lliont/lion32/llcc/clib.asm

data
export _fstatus
align 4
LABELV _fstatus
byte 4 1
byte 4 1
byte 4 1
byte 4 1
byte 4 1
skip 48
export _cnt
align 4
LABELV _cnt
byte 4 0
export _arg1
align 1
LABELV _arg1
byte 1 42
byte 1 0
export FMEMORG
align 4
LABELV FMEMORG
byte 4 18532
export FMEMLOWL
align 4
LABELV FMEMLOWL
byte 4 18538
export ftab
align 4
LABELV ftab
byte 4 18600
export abort
code
proc abort 0 0
CNSTI4 0
RETI4
LABELV $1
endproc abort 0 0
export parse
proc parse 48 4
ADDRLP4 0
CNSTI4 1
ASGNI4
LABELV $3
ADDRLP4 0
INDIRI4
CNSTI4 2
LSHI4
ADDRGP4 _vec
ADDP4
CNSTP4 0
ASGNP4
LABELV $4
ADDRLP4 0
ADDRLP4 0
INDIRI4
CNSTI4 1
ADDI4
ASGNI4
ADDRLP4 0
INDIRI4
CNSTI4 12
LTI4 $3
ADDRLP4 8
CNSTI4 0
ASGNI4
ADDRLP4 0
ADDRLP4 8
INDIRI4
ASGNI4
ADDRLP4 4
ADDRLP4 8
INDIRI4
ASGNI4
ADDRGP4 $8
JUMPV
LABELV $7
ADDRLP4 0
ADDRLP4 0
INDIRI4
CNSTI4 1
ADDI4
ASGNI4
LABELV $8
ADDRLP4 12
ADDRLP4 0
INDIRI4
ADDRGP4 cmdlbuf
INDIRP4
ADDP4
INDIRI1
CVII4 1
ASGNI4
ADDRLP4 12
INDIRI4
CNSTI4 13
EQI4 $10
ADDRLP4 12
INDIRI4
CNSTI4 32
NEI4 $7
LABELV $10
ADDRGP4 $12
JUMPV
LABELV $11
ADDRLP4 4
INDIRI4
ADDRGP4 clbuf
ADDP4
ADDRLP4 0
INDIRI4
ADDRGP4 cmdlbuf
INDIRP4
ADDP4
INDIRI1
ASGNI1
ADDRLP4 16
CNSTI4 1
ASGNI4
ADDRLP4 4
ADDRLP4 4
INDIRI4
ADDRLP4 16
INDIRI4
ADDI4
ASGNI4
ADDRLP4 0
ADDRLP4 0
INDIRI4
ADDRLP4 16
INDIRI4
ADDI4
ASGNI4
LABELV $12
ADDRLP4 0
INDIRI4
ADDRGP4 cmdlbuf
INDIRP4
ADDP4
INDIRI1
CVII4 1
CNSTI4 13
EQI4 $14
ADDRLP4 0
INDIRI4
CNSTI4 80
LTI4 $11
LABELV $14
ADDRLP4 20
ADDRLP4 4
INDIRI4
CNSTI4 1
ADDI4
ASGNI4
ADDRLP4 4
ADDRLP4 20
INDIRI4
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
import _free
import exit
import main
bss
export _buf_str
align 1
LABELV _buf_str
skip 24
import read
export fnameb
align 1
LABELV fnameb
skip 14
export cmdlbuf
align 4
LABELV cmdlbuf
skip 4
export _memptr
align 4
LABELV _memptr
skip 4
export clbuf
align 1
LABELV clbuf
skip 81
export _vec
align 4
LABELV _vec
skip 48
export _fcnt
align 4
LABELV _fcnt
skip 4
import _fputc
import _alloc
import ftell
import fsize
import fseek
import _fopen
import itof
import ftoi
import argcnt
import argbase
import putchar
