lliont/lion32/llcc/clibo.asm

ORG 0
_XY EQU $4868
FMEMORG EQU $4864
MOVR.D (_cmdlbuf),A7
JRSR __main
POP A0
RET
__fstatus:
DD $00000001
DD $00000001
DD $00000001
DD $00000001
DD $00000001
DSW 48
__cnt:
DD $00000000
__arg1:
DB 42
DB 0
_FMEMORG:
DD $00004864
_FMEMLOWL:
DD $0000486a
_ftab:
DD $000048a8
_abort:
PUSH A5
PUSH A6
PUSH A7
MOV.D A5,A7
MOV A7,SP
MOV.D A6,A7
SUB.D SP,0
PUSH $00000000
JR _abort_end
_$1:
_abort_end:
POP A4
MOV SP,A7
POP A7
POP A6
POP A5
POP A1
PUSH A4
JMP A1
_parse:
PUSH A5
PUSH A6
PUSH A7
MOV.D A5,A7
MOV A7,SP
MOV.D A6,A7
SUB.D A6,4
SUB.D SP,52
MOV.D A1,A6
  MOV.D A2,A1
  MOVI A1,$00000001
MOV.D (A2),A1
_$3:
MOV.D A1,A6
  MOV.D A2,(A1)
  MOVI A1,$00000002
SLA.D A2,A1
PUSH A2
GADR A1,__vec
POP A2
ADD.D A1,A2
  MOV.D A2,A1
  MOVI A1,$00000000
MOV.D (A2),A1
_$4:
MOV.D A1,A6
PUSH A1
MOV.D A1,A6
  MOV.D A2,(A1)
  MOVI A1,$00000001
ADD.D A1,A2
POP A2
MOV.D (A2),A1
MOV.D A1,A6
  MOV.D A2,(A1)
  MOVI A1,$0000000c
CMP.D A2,A1
JRL _$3
MOV.D A1,A6
SUBI A1,8
  MOV.D A2,A1
  MOVI A1,$00000000
MOV.D (A2),A1
MOV.D A1,A6
PUSH A1
MOV.D A1,A6
SUBI A1,8
  MOV.D A1,(A1)
POP A2
MOV.D (A2),A1
MOV.D A1,A6
SUBI A1,4
PUSH A1
MOV.D A1,A6
SUBI A1,8
  MOV.D A1,(A1)
POP A2
MOV.D (A2),A1
GADR A1,_$8
JMP A1
_$7:
MOV.D A1,A6
PUSH A1
MOV.D A1,A6
  MOV.D A2,(A1)
  MOVI A1,$00000001
ADD.D A1,A2
POP A2
MOV.D (A2),A1
_$8:
MOV.D A1,A6
SUBI A1,12
PUSH A1
MOV.D A1,A6
PUSH (A1)
GADR A1,_cmdlbuf
  MOV.D A1,(A1)
POP A2
ADD.D A1,A2
CMOV.B A2,(A1)
  MOV.D A1,A2
SEX.B A1
POP A2
MOV.D (A2),A1
MOV.D A1,A6
SUBI A1,12
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
  MOV.D A2,A1
  MOVI A1,$00000000
MOV.D (A2),A1
_$381:
MOV.D A1,A6
PUSH (A1)
JR _isxdigit_end
_$378:
_isxdigit_end:
POP A4
MOV SP,A7
POP A7
POP A6
POP A5
POP A1
PUSH A4
JMP A1
__buf_str:
DSW 24
_fnameb:
DSW 14
_cmdlbuf:
DSW 4
__memptr:
DSW 4
_clbuf:
DS 81
__vec:
DSW 48
__fcnt:
DSW 4
__END: RET
