lliont/lion32/llcc/matho.asm

ORG 0
_XY EQU $4868
FMEMORG EQU $4864
MOVR.D (_cmdlbuf),A7
JRSR __main
POP A0
RET
_PI:
DD $40490fdb
_trunc:
PUSH A5
PUSH A6
PUSH A7
MOV.D A5,A7
MOV A7,SP
MOV.D A6,A7
SUB.D SP,4
MOV.D A1,A6
PUSH A1
MOV.D A1,A5
  MOV.D A3,(A1)
JRSR __ftoi
POP A1
POP A2
MOV.D (A2),A1
MOV.D A1,A6
  MOV.D A4,(A1)
JRSR __itof
JR _trunc_end
_$1:
_trunc_end:
POP A4
MOV SP,A7
POP A7
POP A6
POP A5
POP A1
PUSH A4
JMP A1
_round:
PUSH A5
PUSH A6
PUSH A7
MOV.D A5,A7
MOV A7,SP
MOV.D A6,A7
SUB.D SP,4
MOV.D A1,A6
PUSH A1
MOV.D A1,A5
  MOV.D A3,(A1)
  MOV.D A1,$3f000000
MOVI A0,11
INT 5
  MOV.D A3,A1
JRSR __ftoi
POP A1
POP A2
MOV.D (A2),A1
MOV.D A1,A6
  MOV.D A4,(A1)
JRSR __itof
JR _round_end
_$2:
_round_end:
POP A4
MOV SP,A7
POP A7
POP A6
POP A5
POP A1
PUSH A4
JMP A1
_fmod:
PUSH A5
PUSH A6
PUSH A7
MOV.D A5,A7
MOV A7,SP
MOV.D A6,A7
SUB.D A6,4
SUB.D SP,12
MOV.D A1,A6
PUSH A1
MOV.D A1,A5
  MOV.D A1,(A1)
POP A2
MOV.D (A2),A1
MOV.D A1,A6
PUSH (A1)
MOV.D A1,A5
SUBI A1,4
  MOV.D A3,(A1)
POP A1
MOVI A0,10
INT 5
MOV.D (A7),A1
MOV.D A1,A6
SUBI A1,4
PUSH A1
GADR A1,_trunc
MOVR.D (_argnum),1
MOVR.D (_argbs),A7
JSR A1
POP A1
POP A2
MOV.D (A2),A1
MOV.D A1,A6
PUSH (A1)
MOV.D A1,A6
SUBI A1,4
PUSH (A1)
MOV.D A1,A5
SUBI A1,4
  MOV.D A1,(A1)
POP A3
MOVI A0,9
INT 5
  MOV.D A3,A1
POP A1
XOR.D A3,$80000000
MOVI A0,11
INT 5
PUSH A1
JR _fmod_end
_$3:
_fmod_end:
POP A4
MOV SP,A7
POP A7
POP A6
POP A5
POP A1
PUSH A4
JMP A1
_sin:
PUSH A5
PUSH A6
PUSH A7
MOV.D A5,A7
MOV A7,SP
MOV.D A6,A7
SUB.D A6,8
SUB.D SP,16
MOV.D A1,A5
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
PUSH (A1)
MOV.D A1,A5
PUSH (A1)
MOV.D A1,A5
  MOV.D A1,(A1)
POP A3
MOVI A0,9
INT 5
POP A3
MOVI A0,11
INT 5
POP A2
MOV.D (A2),A1
MOV.D A1,A6
SUB.D A1,20
PUSH A1
MOV.D A1,A6
SUBI A1,12
PUSH (A1)
MOV.D A1,A5
SUBI A1,4
PUSH (A1)
MOV.D A1,A5
SUBI A1,4
  MOV.D A1,(A1)
POP A3
MOVI A0,9
INT 5
PUSH A1
MOV.D A1,A6
SUBI A1,8
  MOV.D A1,(A1)
POP A3
MOVI A0,11
INT 5
PUSH A1
MOV.D A1,A6
SUBI A1,12
  MOV.D A1,(A1)
POP A3
MOVI A0,11
INT 5
  MOV.D A3,A1
  MOV.D A1,$358637bd
MOVI A0,11
INT 5
  MOV.D A3,A1
POP A1
MOVI A0,10
INT 5
POP A2
MOV.D (A2),A1
MOV.D A1,A6
SUB.D A1,24
PUSH A1
MOV.D A1,A6
PUSH (A1)
MOV.D A1,A6
SUBI A1,4
  MOV.D A1,(A1)
POP A2
XOR.D A2,A1
PUSH A2
MOV.D A1,A6
SUB.D A1,20
  MOV.D A3,(A1)
JRSR __ftoi
POP A1
POP A2
OR.D A2,A1
  MOV.D A1,A2
POP A2
MOV.D (A2),A1
MOV.D A1,A6
SUB.D A1,16
PUSH (A1)
MOV.D A1,A6
SUB.D A1,24
  MOV.D A4,(A1)
JRSR __itof
POP A1
POP A3
MOVI A0,11
INT 5
PUSH A1
GADR A1,_PI
  MOV.D A1,(A1)
POP A3
MOVI A0,9
INT 5
  MOV.D A3,$40000000
MOVI A0,10
INT 5
PUSH A1
JR _atan2_end
_$27:
_atan2_end:
POP A4
MOV SP,A7
POP A7
POP A6
POP A5
POP A1
PUSH A4
JMP A1
__END: RET
