lliont/lion32/llcc/tmo.asm

ORG 0
_XY EQU $4868
FMEMORG EQU $4864
 MOVR.D (_cmdlbuf),A7
 JRSR __main
 POP A0
 RET

; data Segment
_side:
 DD $40700000
_real:
 DD $bf000000
_imag:
 DD $00000000
; code Segment

_main:
 PUSH A5
 PUSH A6
 PUSH A7
 MOV.D A5,A7
 MOV A7,SP
 MOV.D A6,A7
 SUB.D A6,12
 SUB.D SP,88
 MOV.D A1,A6
 SUBI A1,12
 PUSH A1
 GADR A1,_scrw
 PUSH A1
 POP A1
 POP A2
 MOV.D (A2),A1
 MOV.D A1,A6
 SUBI A1,12
 PUSH A1
 POP A1
 PUSH (A1)
 PUSH $00000140
 POP A1
 POP A2
 MOV.D (A2),A1
 MOV.D A1,A6
 SUB.D A1,16
 PUSH A1
 GADR A1,_scrh
 PUSH A1
 POP A1
 POP A2
 MOV.D (A2),A1
 MOV.D A1,A6
 SUB.D A1,16
 PUSH A1
 POP A1
 PUSH (A1)
 PUSH $000000c8
 POP A1
 POP A2
 MOV.D (A2),A1
 GADR A1,_maxiter
 PUSH A1
 PUSH $000000fe
 POP A1
 POP A2
 MOV.D (A2),A1
 MOV.D A1,A6
 SUB.D A1,20
 PUSH A1
 GADR A1,_aspect
 PUSH A1
 POP A1
 POP A2
 MOV.D (A2),A1
 MOV.D A1,A6
 SUB.D A1,24
 PUSH A1
 MOV.D A1,A6
 SUBI A1,12
 PUSH A1
 POP A1
 PUSH (A1)
 POP A1
 PUSH (A1)
 POP A4
 JRSR __itof
 POP A1
 POP A2
 MOV.D (A2),A1
 MOV.D A1,A6
 SUB.D A1,20
 PUSH A1
 POP A1
 PUSH (A1)
 MOV.D A1,A6
 SUB.D A1,24
 PUSH A1
 POP A1
 PUSH (A1)
 MOV.D A1,A6
 SUB.D A1,16
 PUSH A1
 POP A1
 PUSH (A1)
 POP A1
 PUSH (A1)
 POP A4
 JRSR __itof
 POP A3
 POP A1
 MOVI A0,10
 INT 5
 PUSH A1
 POP A1
 POP A2
 MOV.D (A2),A1
 MOV.D A1,A6
 SUBI A1,8
 PUSH A1
 PUSH $00000008
 POP A1
 POP A2
 MOV.D (A2),A1
 GADR A1,_key
 PUSH A1
 PUSH $00000000
 POP A1
 POP A2
 MOV.D (A2),A1
 MOV.D A1,A6
 SUB.D A1,28
 PUSH A1
 GADR A1,_side
 PUSH A1
 POP A1
 PUSH (A1)
 POP A1
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
 DSW 4
_scrh:
 DSW 4
_scrw:
 DSW 4
_lcolr:
 DSW 4
_tim2:
 DSW 4
_tim1:
 DSW 4
_colr:
 DSW 4
_counter:
 DSW 4
_key:
 DSW 4
_b:
 DSW 4
_a:
 DSW 4
_zi:
 DSW 4
_zr:
 DSW 4
_cr:
 DSW 4
_ci:
 DSW 4
_im:
 DSW 4
_re:
 DSW 4
_dist:
 DSW 4
_aspect:
 DSW 4
; lit Segment
_$16:
 DB 37
 DB 100
 DB 0
__END: RET
