lliont/lion32/VHDL/LPLL32.vhd

-- megafunction wizard: %PLL Intel FPGA IP v18.1%
-- GENERATION: XML
-- LPLL32.vhd

-- Generated using ACDS version 18.1 646

library IEEE;
use IEEE.std_logic_1164.all;
use IEEE.numeric_std.all;

entity LPLL32 is
	port (
		refclk   : in  std_logic := '0'; --  refclk.clk
		rst      : in  std_logic := '0'; --   reset.reset
		outclk_0 : out std_logic;        -- outclk0.clk
		outclk_1 : out std_logic;        -- outclk1.clk
		outclk_2 : out std_logic;        -- outclk2.clk
		outclk_3 : out std_logic         -- outclk3.clk
	);
end entity LPLL32;

architecture rtl of LPLL32 is
	component LPLL32_0002 is
		port (
			refclk   : in  std_logic := 'X'; -- clk
			rst      : in  std_logic := 'X'; -- reset
			outclk_0 : out std_logic;        -- clk
			outclk_1 : out std_logic;        -- clk
			outclk_2 : out std_logic;        -- clk
			outclk_3 : out std_logic;        -- clk
			locked   : out std_logic         -- export
		);
	end component LPLL32_0002;

begin

	lpll32_inst : component LPLL32_0002
		port map (
			refclk   => refclk,   --  refclk.clk
			rst      => rst,      --   reset.reset
			outclk_0 => outclk_0, -- outclk0.clk
			outclk_1 => outclk_1, -- outclk1.clk
			outclk_2 => outclk_2, -- outclk2.clk
			outclk_3 => outclk_3, -- outclk3.clk
			locked   => open      -- (terminated)
		);

end architecture rtl; -- of LPLL32
-- Retrieval info: <?xml version="1.0"?>
--<!--
--	Generated by Altera MegaWizard Launcher Utility version 1.0
--	************************************************************
--	THIS IS A WIZARD-GENERATED FILE. DO NOT EDIT THIS FILE!
--	************************************************************
--	Copyright (C) 1991-2022 Altera Corporation
--	Any megafunction design, and related net list (encrypted or decrypted),
--	support information, device programming or simulation file, and any other
--	associated documentation or information provided by Altera or a partner
--	under Altera's Megafunction Partnership Program may be used only to
--	program PLD devices (but not masked PLD devices) from Altera.  Any other
--	use of such megafunction design, net list, support information, device
--	programming or simulation file, or any other related documentation or
--	information is prohibited for any other purpose, including, but not
--	limited to modification, reverse engineering, de-compiling, or use with
--	any other silicon devices, unless such use is explicitly licensed under
--	a separate agreement with Altera or a megafunction partner.  Title to
--	the intellectual property, including patents, copyrights, trademarks,
--	trade secrets, or maskworks, embodied in any such megafunction design,
--	net list, support information, device programming or simulation file, or
--	any other related documentation or information provided by Altera or a
--	megafunction partner, remains with Altera, the megafunction partner, or
--	their respective licensors.  No other licenses, including any licenses
--	needed under any third party's intellectual property, are provided herein.
---->
-- Retrieval info: <instance entity-name="altera_pll" version="18.1" >
-- Retrieval info: 	<generic name="debug_print_output" value="false" />
-- Retrieval info: 	<generic name="debug_use_rbc_taf_method" value="false" />
-- Retrieval info: 	<generic name="device_family" value="Cyclone V" />
-- Retrieval info: 	<generic name="device" value="5CEBA2F17A7" />
-- Retrieval info: 	<generic name="gui_device_speed_grade" value="1" />
-- Retrieval info: 	<generic name="gui_pll_mode" value="Integer-N PLL" />
-- Retrieval info: 	<generic name="gui_reference_clock_frequency" value="50.0" />
-- Retrieval info: 	<generic name="gui_channel_spacing" value="0.0" />
-- Retrieval info: 	<generic name="gui_operation_mode" value="normal" />
-- Retrieval info: 	<generic name="gui_feedback_clock" value="Global Clock" />
-- Retrieval info: 	<generic name="gui_fractional_cout" value="32" />
-- Retrieval info: 	<generic name="gui_dsm_out_sel" value="1st_order" />
-- Retrieval info: 	<generic name="gui_use_locked" value="false" />
-- Retrieval info: 	<generic name="gui_en_adv_params" value="false" />
-- Retrieval info: 	<generic name="gui_number_of_clocks" value="4" />
-- Retrieval info: 	<generic name="gui_multiply_factor" value="1" />
-- Retrieval info: 	<generic name="gui_frac_multiply_factor" value="1" />
-- Retrieval info: 	<generic name="gui_divide_factor_n" value="1" />
-- Retrieval info: 	<generic name="gui_cascade_counter0" value="false" />
-- Retrieval info: 	<generic name="gui_output_clock_frequency0" value="50.0" />
-- Retrieval info: 	<generic name="gui_divide_factor_c0" value="1" />
-- Retrieval info: 	<generic name="gui_actual_output_clock_frequency0" value="0 MHz" />
-- Retrieval info: 	<generic name="gui_ps_units0" value="degrees" />
-- Retrieval info: 	<generic name="gui_phase_shift0" value="0" />
-- Retrieval info: 	<generic name="gui_phase_shift_deg0" value="0.0" />
-- Retrieval info: 	<generic name="gui_actual_phase_shift0" value="0" />
-- Retrieval info: 	<generic name="gui_duty_cycle0" value="50" />
-- Retrieval info: 	<generic name="gui_cascade_counter1" value="false" />
-- Retrieval info: 	<generic name="gui_output_clock_frequency1" value="50.0" />
-- Retrieval info: 	<generic name="gui_divide_factor_c1" value="1" />
-- Retrieval info: 	<generic name="gui_actual_output_clock_frequency1" value="0 MHz" />
-- Retrieval info: 	<generic name="gui_ps_units1" value="degrees" />
-- Retrieval info: 	<generic name="gui_phase_shift1" value="0" />
-- Retrieval info: 	<generic name="gui_phase_shift_deg1" value="180.0" />
-- Retrieval info: 	<generic name="gui_actual_phase_shift1" value="0" />
-- Retrieval info: 	<generic name="gui_duty_cycle1" value="50" />
-- Retrieval info: 	<generic name="gui_cascade_counter2" value="false" />
-- Retrieval info: 	<generic name="gui_output_clock_frequency2" value="40.0" />
-- Retrieval info: 	<generic name="gui_divide_factor_c2" value="1" />
-- Retrieval info: 	<generic name="gui_actual_output_clock_frequency2" value="0 MHz" />
-- Retrieval info: 	<generic name="gui_ps_units2" value="degrees" />
-- Retrieval info: 	<generic name="gui_phase_shift2" value="0" />
-- Retrieval info: 	<generic name="gui_phase_shift_deg2" value="0.0" />
-- Retrieval info: 	<generic name="gui_actual_phase_shift2" value="0" />
-- Retrieval info: 	<generic name="gui_duty_cycle2" value="50" />
-- Retrieval info: 	<generic name="gui_cascade_counter3" value="false" />
-- Retrieval info: 	<generic name="gui_output_clock_frequency3" value="40.0" />
-- Retrieval info: 	<generic name="gui_divide_factor_c3" value="1" />
-- Retrieval info: 	<generic name="gui_actual_output_clock_frequency3" value="0 MHz" />
-- Retrieval info: 	<generic name="gui_ps_units3" value="degrees" />
-- Retrieval info: 	<generic name="gui_phase_shift3" value="0" />
-- Retrieval info: 	<generic name="gui_phase_shift_deg3" value="180.0" />
-- Retrieval info: 	<generic name="gui_actual_phase_shift3" value="0" />
-- Retrieval info: 	<generic name="gui_duty_cycle3" value="50" />
-- Retrieval info: 	<generic name="gui_cascade_counter4" value="false" />
-- Retrieval info: 	<generic name="gui_output_clock_frequency4" value="100.0" />
-- Retrieval info: 	<generic name="gui_divide_factor_c4" value="1" />
-- Retrieval info: 	<generic name="gui_actual_output_clock_frequency4" value="0 MHz" />
-- Retrieval info: 	<generic name="gui_ps_units4" value="ps" />
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
-- Retrieval info: 	<generic name="gui_actual_output_clock_frequency15" value="0 MHz" />
-- Retrieval info: 	<generic name="gui_ps_units15" value="ps" />
-- Retrieval info: 	<generic name="gui_phase_shift15" value="0" />
-- Retrieval info: 	<generic name="gui_phase_shift_deg15" value="0.0" />
-- Retrieval info: 	<generic name="gui_actual_phase_shift15" value="0" />
-- Retrieval info: 	<generic name="gui_duty_cycle15" value="50" />
-- Retrieval info: 	<generic name="gui_cascade_counter16" value="false" />
-- Retrieval info: 	<generic name="gui_output_clock_frequency16" value="100.0" />
-- Retrieval info: 	<generic name="gui_divide_factor_c16" value="1" />
-- Retrieval info: 	<generic name="gui_actual_output_clock_frequency16" value="0 MHz" />
-- Retrieval info: 	<generic name="gui_ps_units16" value="ps" />
-- Retrieval info: 	<generic name="gui_phase_shift16" value="0" />
-- Retrieval info: 	<generic name="gui_phase_shift_deg16" value="0.0" />
-- Retrieval info: 	<generic name="gui_actual_phase_shift16" value="0" />
-- Retrieval info: 	<generic name="gui_duty_cycle16" value="50" />
-- Retrieval info: 	<generic name="gui_cascade_counter17" value="false" />
-- Retrieval info: 	<generic name="gui_output_clock_frequency17" value="100.0" />
-- Retrieval info: 	<generic name="gui_divide_factor_c17" value="1" />
-- Retrieval info: 	<generic name="gui_actual_output_clock_frequency17" value="0 MHz" />
-- Retrieval info: 	<generic name="gui_ps_units17" value="ps" />
-- Retrieval info: 	<generic name="gui_phase_shift17" value="0" />
-- Retrieval info: 	<generic name="gui_phase_shift_deg17" value="0.0" />
-- Retrieval info: 	<generic name="gui_actual_phase_shift17" value="0" />
-- Retrieval info: 	<generic name="gui_duty_cycle17" value="50" />
-- Retrieval info: 	<generic name="gui_pll_auto_reset" value="On" />
-- Retrieval info: 	<generic name="gui_pll_bandwidth_preset" value="Auto" />
-- Retrieval info: 	<generic name="gui_en_reconf" value="false" />
-- Retrieval info: 	<generic name="gui_en_dps_ports" value="false" />
-- Retrieval info: 	<generic name="gui_en_phout_ports" value="false" />
-- Retrieval info: 	<generic name="gui_phout_division" value="1" />
-- Retrieval info: 	<generic name="gui_mif_generate" value="false" />
-- Retrieval info: 	<generic name="gui_enable_mif_dps" value="false" />
-- Retrieval info: 	<generic name="gui_dps_cntr" value="C0" />
-- Retrieval info: 	<generic name="gui_dps_num" value="1" />
-- Retrieval info: 	<generic name="gui_dps_dir" value="Positive" />
-- Retrieval info: 	<generic name="gui_refclk_switch" value="false" />
-- Retrieval info: 	<generic name="gui_refclk1_frequency" value="100.0" />
-- Retrieval info: 	<generic name="gui_switchover_mode" value="Automatic Switchover" />
-- Retrieval info: 	<generic name="gui_switchover_delay" value="0" />
-- Retrieval info: 	<generic name="gui_active_clk" value="false" />
-- Retrieval info: 	<generic name="gui_clk_bad" value="false" />
-- Retrieval info: 	<generic name="gui_enable_cascade_out" value="false" />
-- Retrieval info: 	<generic name="gui_cascade_outclk_index" value="0" />
-- Retrieval info: 	<generic name="gui_enable_cascade_in" value="false" />
-- Retrieval info: 	<generic name="gui_pll_cascading_mode" value="Create an adjpllin signal to connect with an upstream PLL" />
-- Retrieval info: </instance>
-- IPFS_FILES : LPLL32.vho
-- RELATED_FILES: LPLL32.vhd, LPLL32_0002.v
