lliont/lion32/llcc/math.asm

data
export PI
align 4
LABELV PI
byte 4 1078530011
export trunc
code
proc trunc 4 0
ADDRLP4 0
ADDRFP4 0
INDIRF4
CVFI4 4
ASGNI4
ADDRLP4 0
INDIRI4
CVIF4 4
RETF4
LABELV $1
endproc trunc 4 0
export round
proc round 4 0
ADDRLP4 0
ADDRFP4 0
INDIRF4
CNSTF4 1056964608
ADDF4
CVFI4 4
ASGNI4
ADDRLP4 0
INDIRI4
CVIF4 4
RETF4
LABELV $2
endproc round 4 0
export fmod
proc fmod 8 4
ADDRLP4 0
ADDRFP4 0
INDIRF4
ASGNF4
ADDRLP4 0
INDIRF4
ADDRFP4 4
INDIRF4
DIVF4
ARGF4
ADDRLP4 4
ADDRGP4 trunc
CALLF4
ASGNF4
ADDRLP4 0
INDIRF4
ADDRLP4 4
INDIRF4
ADDRFP4 4
INDIRF4
MULF4
SUBF4
RETF4
LABELV $3
endproc fmod 8 4
export sin
proc sin 8 8
ADDRFP4 0
INDIRF4
ARGF4
CNSTF4 1073741824
ADDRGP4 PI
INDIRF4
MULF4
ARGF4
ADDRLP4 0
ADDRGP4 fmod
CALLF4
ASGNF4
ADDRLP4 0
INDIRF4
ARGF4
ADDRLP4 4
ADDRGP4 _sin
CALLF4
ASGNF4
ADDRLP4 4
INDIRF4
RETF4
LABELV $4
endproc sin 8 8
export cos
proc cos 16 8
ADDRFP4 0
INDIRF4
ARGF4
ADDRLP4 0
CNSTF4 1073741824
ASGNF4
ADDRLP4 4
ADDRGP4 PI
INDIRF4
ASGNF4
ADDRLP4 0
INDIRF4
ADDRLP4 4
INDIRF4
MULF4
ARGF4
ADDRLP4 8
ADDRGP4 fmod
CALLF4
ASGNF4
ADDRLP4 4
INDIRF4
ADDRLP4 0
INDIRF4
DIVF4
ADDRLP4 8
INDIRF4
SUBF4
ARGF4
ADDRLP4 12
ADDRGP4 _sin
CALLF4
ASGNF4
ADDRLP4 12
INDIRF4
RETF4
LABELV $5
endproc cos 16 8
export log2
proc log2 44 0
ADDRLP4 8
CNSTF4 3206623816
ASGNF4
ADDRLP4 12
CNSTF4 1069270419
ASGNF4
ADDRLP4 4
ADDRFP4 0
INDIRF4
ASGNF4
ADDRLP4 36
ADDRLP4 4
INDIRU4
ASGNU4
ADDRLP4 20
ADDRLP4 36
INDIRU4
CNSTU4 2139095040
BANDU4
CNSTI4 23
RSHU4
CVUI4 4
ASGNI4
ADDRLP4 32
ADDRLP4 36
INDIRU4
CNSTU4 4194304
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
ADDF4
DIVF4
ASGNF4
ADDRLP4 24
ADDRLP4 0
INDIRI4
ADDRLP4 4
INDIRI4
BXORI4
ADDRLP4 20
INDIRF4
CVFI4 4
BORI4
ASGNI4
ADDRLP4 16
INDIRF4
ADDRLP4 24
INDIRI4
CVIF4 4
ADDF4
ADDRGP4 PI
INDIRF4
MULF4
CNSTF4 1073741824
DIVF4
RETF4
LABELV $27
endproc atan2 48 4
import exp
import sqrt
import _sin
