lliont/lion32/llcc/tm.asm

data
export side
align 4
LABELV side
byte 4 1081081856
export real
align 4
LABELV real
byte 4 3204448256
export imag
align 4
LABELV imag
byte 4 0
export main
code
proc main 76 12
ADDRLP4 12
ADDRGP4 scrw
ASGNP4
ADDRLP4 12
INDIRP4
CNSTI4 320
ASGNI4
ADDRLP4 16
ADDRGP4 scrh
ASGNP4
ADDRLP4 16
INDIRP4
CNSTI4 200
ASGNI4
ADDRGP4 maxiter
CNSTI4 254
ASGNI4
ADDRLP4 20
ADDRGP4 aspect
ASGNP4
ADDRLP4 24
ADDRLP4 12
INDIRP4
INDIRI4
CVIF4 4
ASGNF4
ADDRLP4 20
INDIRP4
ADDRLP4 24
INDIRF4
ADDRLP4 16
INDIRP4
INDIRI4
CVIF4 4
DIVF4
ASGNF4
ADDRLP4 8
CNSTI4 8
ASGNI4
ADDRGP4 key
CNSTI4 0
ASGNI4
ADDRLP4 28
ADDRGP4 side
INDIRF4
ASGNF4
ADDRGP4 dist
ADDRLP4 28
INDIRF4
ADDRLP4 24
INDIRF4
DIVF4
ASGNF4
ADDRLP4 32
CNSTF4 1073741824
ASGNF4
ADDRGP4 re
ADDRGP4 real
INDIRF4
ADDRLP4 28
INDIRF4
ADDRLP4 32
INDIRF4
DIVF4
SUBF4
ASGNF4
ADDRGP4 im
ADDRGP4 imag
INDIRF4
ADDRLP4 28
INDIRF4
ADDRLP4 20
INDIRP4
INDIRF4
DIVF4
ADDRLP4 32
INDIRF4
DIVF4
SUBF4
ASGNF4
CNSTI4 24
ARGI4
CNSTI4 1
ARGI4
ADDRGP4 IOout
CALLI4
pop
CNSTI4 0
ARGI4
CNSTI4 15
ARGI4
ADDRGP4 Screen
CALLI4
pop
ADDRGP4 Cls
CALLI4
pop
ADDRLP4 36
ADDRGP4 Timer
CALLI4
ASGNI4
ADDRGP4 tim1
ADDRLP4 36
INDIRI4
ASGNI4
ADDRLP4 40
CNSTI4 0
ASGNI4
ADDRGP4 lcolr
ADDRLP4 40
INDIRI4
ASGNI4
ADDRLP4 4
ADDRLP4 40
INDIRI4
ASGNI4
ADDRGP4 $5
JUMPV
LABELV $2
ADDRGP4 ci
ADDRGP4 im
INDIRF4
ADDRLP4 4
INDIRI4
CVIF4 4
ADDRGP4 dist
INDIRF4
MULF4
ADDF4
ASGNF4
ADDRLP4 0
CNSTI4 0
ASGNI4
ADDRGP4 $9
JUMPV
LABELV $6
ADDRLP4 44
ADDRGP4 cr
ASGNP4
ADDRLP4 44
INDIRP4
ADDRGP4 re
INDIRF4
ADDRLP4 0
INDIRI4
CVIF4 4
ADDRGP4 dist
INDIRF4
MULF4
ADDF4
ASGNF4
ADDRGP4 zr
ADDRLP4 44
INDIRP4
INDIRF4
ASGNF4
ADDRGP4 zi
ADDRGP4 ci
INDIRF4
ASGNF4
ADDRGP4 counter
CNSTI4 64
ASGNI4
LABELV $10
ADDRLP4 48
ADDRGP4 a
ASGNP4
ADDRLP4 52
ADDRGP4 zr
ASGNP4
ADDRLP4 56
ADDRLP4 52
INDIRP4
INDIRF4
ASGNF4
ADDRLP4 48
INDIRP4
ADDRLP4 56
INDIRF4
ADDRLP4 56
INDIRF4
MULF4
ASGNF4
ADDRLP4 60
ADDRGP4 b
ASGNP4
ADDRLP4 64
ADDRGP4 zi
ASGNP4
ADDRLP4 68
ADDRLP4 64
INDIRP4
INDIRF4
ASGNF4
ADDRLP4 60
INDIRP4
ADDRLP4 68
INDIRF4
ADDRLP4 68
INDIRF4
MULF4
ASGNF4
ADDRLP4 64
INDIRP4
CNSTF4 1073741824
ADDRLP4 56
INDIRF4
MULF4
ADDRLP4 68
INDIRF4
MULF4
ADDRGP4 ci
INDIRF4
ADDF4
ASGNF4
ADDRLP4 52
INDIRP4
ADDRLP4 48
INDIRP4
INDIRF4
ADDRGP4 cr
INDIRF4
ADDF4
ADDRLP4 60
INDIRP4
INDIRF4
SUBF4
ASGNF4
ADDRLP4 72
ADDRGP4 counter
ASGNP4
ADDRLP4 72
INDIRP4
ADDRLP4 72
INDIRP4
INDIRI4
CNSTI4 1
SUBI4
ASGNI4
LABELV $11
ADDRGP4 counter
INDIRI4
CNSTI4 1
LEI4 $13
CNSTF4 1090519040
ADDRGP4 a
INDIRF4
ADDRGP4 b
INDIRF4
ADDF4
GTF4 $10
LABELV $13
ADDRLP4 48
ADDRGP4 colr
ASGNP4
ADDRLP4 48
INDIRP4
CNSTI4 65
ADDRGP4 counter
INDIRI4
SUBI4
ASGNI4
ADDRGP4 lcolr
INDIRI4
ADDRLP4 48
INDIRP4
INDIRI4
EQI4 $14
CNSTI4 0
ARGI4
ADDRGP4 colr
INDIRI4
ARGI4
ADDRGP4 Screen
CALLI4
pop
ADDRGP4 lcolr
ADDRGP4 colr
INDIRI4
ASGNI4
LABELV $14
ADDRLP4 0
INDIRI4
ARGI4
ADDRLP4 4
INDIRI4
ARGI4
CNSTI4 1
ARGI4
ADDRGP4 Plot
CALLI4
pop
ADDRLP4 0
INDIRI4
ARGI4
ADDRGP4 scrh
INDIRI4
ADDRLP4 4
INDIRI4
SUBI4
ARGI4
CNSTI4 1
ARGI4
ADDRGP4 Plot
CALLI4
pop
LABELV $7
ADDRLP4 0
ADDRLP4 0
INDIRI4
CNSTI4 1
ADDI4
ASGNI4
LABELV $9
ADDRLP4 0
INDIRI4
ADDRGP4 scrw
INDIRI4
LTI4 $6
LABELV $3
ADDRLP4 4
ADDRLP4 4
INDIRI4
CNSTI4 1
ADDI4
ASGNI4
LABELV $5
ADDRLP4 44
CNSTI4 1
ASGNI4
ADDRLP4 4
INDIRI4
ADDRLP4 44
INDIRI4
LSHI4
ADDRLP4 44
INDIRI4
SUBI4
ADDRGP4 scrh
INDIRI4
LTI4 $2
ADDRLP4 48
ADDRGP4 Timer
CALLI4
ASGNI4
ADDRGP4 tim2
ADDRLP4 48
INDIRI4
ASGNI4
ADDRLP4 52
ADDRGP4 tim1
ASGNP4
ADDRLP4 52
INDIRP4
ADDRGP4 tim2
INDIRI4
ADDRLP4 52
INDIRP4
INDIRI4
SUBI4
ASGNI4
CNSTI4 0
ARGI4
CNSTI4 30
ARGI4
ADDRGP4 Screen
CALLI4
pop
CNSTI4 21
ARGI4
CNSTI4 46
ARGI4
ADDRGP4 PosYX
CALLI4
pop
ADDRGP4 $16
ARGP4
ADDRGP4 tim1
INDIRI4
ARGI4
ADDRGP4 printf
CALLI4
pop
ADDRGP4 $18
JUMPV
LABELV $17
ADDRLP4 56
ADDRGP4 Inkey
CALLI4
ASGNI4
ADDRGP4 key
ADDRLP4 56
INDIRI4
ASGNI4
LABELV $18
ADDRGP4 key
INDIRI4
CNSTI4 32
NEI4 $17
LABELV $1
endproc main 76 12
import Inkey
import printf
import PosYX
import Plot
import Timer
import Cls
import Screen
import IOout
bss
export maxiter
align 4
LABELV maxiter
skip 4
export scrh
align 4
LABELV scrh
skip 4
export scrw
align 4
LABELV scrw
skip 4
export lcolr
align 4
LABELV lcolr
skip 4
export tim2
align 4
LABELV tim2
skip 4
export tim1
align 4
LABELV tim1
skip 4
export colr
align 4
LABELV colr
skip 4
export counter
align 4
LABELV counter
skip 4
export key
align 4
LABELV key
skip 4
export b
align 4
LABELV b
skip 4
export a
align 4
LABELV a
skip 4
export zi
align 4
LABELV zi
skip 4
export zr
align 4
LABELV zr
skip 4
export cr
align 4
LABELV cr
skip 4
export ci
align 4
LABELV ci
skip 4
export im
align 4
LABELV im
skip 4
export re
align 4
LABELV re
skip 4
export dist
align 4
LABELV dist
skip 4
export aspect
align 4
LABELV aspect
skip 4
import _fputc
import _alloc
import ftell
import fsize
import fseek
import fopen
import _fopen
import itof
import ftoi
import argcnt
import argbase
import strcpy
import putchar
lit
align 1
LABELV $16
byte 1 37
byte 1 100
byte 1 0
