lliont/lion32/llcc/math.h

const float PI  = 3.14159265359f;
float sin(float f);
float _sin(float f);
float cos(float f);
float sqrt(float f);
float exp(float f);
float log2(float f);
float log(float f);
float fastpow2(float f);
float pow(float x, float p);
float round(float f);
float atan2( float y, float x );
float atan( float x );
float fabs(float f);
