lliont/lion32/llcc/syslib.h

#define Vbase  32768
#define XYbase 98304
#define PCMbase 98304
#define SCOL 0x4847
#define FCOL 0x485d
#define BCOL 0x485c
#define CIRCX 0x484A
#define CIRCY 0x484C

#define PLOTM 0x484E
#define COLTBL 61152
#define SPRBASE 16384
