lliont/lion32/Lionc/testsys1.c

#include "stdio.h"
#include "clib.h"
#include "syslib.h"

//char fn[12];
char spr[]={  
 0xFF, 0xFF, 0xFF, 0xCC, 0xCF, 0xFF, 0xFF, 0xFF,
 0xFF, 0xFF, 0xFC, 0xCC, 0xCC, 0xFF, 0xFF, 0xFF,
 0xFF, 0xFF, 0xCC, 0xCC, 0xCC, 0xCF, 0xFF, 0xFF,
 0xFF, 0xFF, 0xCC, 0xCC, 0xCC, 0xCF, 0xFF, 0xFF,
 0xFF, 0xFF, 0xCF, 0xFC, 0xFF, 0xCF, 0xFF, 0xFF,
 0xFF, 0x7F, 0xFF, 0x3C, 0x3F, 0xFF, 0x7F, 0xFF,
 0xF7, 0x77, 0xFF, 0x3C, 0x3F, 0xF7, 0x77, 0xFF,
 0xF7, 0x37, 0xFF, 0x3C, 0x3F, 0xF7, 0x37, 0xFF,
 0xF7, 0x37, 0xF3, 0x3C, 0x33, 0xF7, 0x37, 0xFF,
 0xF7, 0x37, 0x33, 0x3C, 0x33, 0x37, 0x37, 0xFF,
 0xF7, 0x33, 0x3F, 0x3C, 0x3F, 0x33, 0x37, 0xFF,
 0xF7, 0x33, 0xFF, 0x3C, 0x3F, 0xF3, 0x37, 0xFF,
 0xF7, 0x37, 0xFF, 0x3F, 0x3F, 0xF7, 0x37, 0xFF,
 0xF7, 0x37, 0xFF, 0xFF, 0xFF, 0xF7, 0x37, 0xFF,
 0xF7, 0x77, 0xFF, 0xFF, 0xFF, 0xF7, 0x77, 0xFF,
 0xFF, 0x7F, 0xFF, 0xFF, 0xFF, 0xFF, 0x7F, 0xFF };

main (int argc, int *argv)
{
	int i,t1,t2,k;
	Set_sprite_data(0,0,spr,0);
	Set_sprite(0,0,1,200,100);
	
	Screen(1,15);
	Cls();
	t1=Timer();
	for (i=0; i<10000; i++) {
		k=i%10;
		PosYX(29, k*5);
		printf("%d",i);
		if (k==9) Scroll_up();
        }
	t2=Timer()-t1;
	k=Inkey();
	PosYX(29, 10);
	printf("%d  %d", t2, k);
	Sound(0,1000,5);
	Plot(550,100,1);
	Line(400,30,550,150);
	do {} while (Isplaying(0));
	Disable_sprite(0);
}
